MrDiamondDog/FlightDeck/firmware/FlightDeck/src/img.hpp

#include <stdint.h>
#include <pgmspace.h>

// 'American', 16x16px
const uint16_t epd_bitmap_American [] PROGMEM = {
	0xffff, 0xffff, 0xffff, 0xffff, 0xffff, 0xffff, 0xffff, 0xffff, 0xffff, 0xffff, 0xffff, 0xffff, 0xffff, 0xffff, 0xffff, 0xffff, 
	0xffff, 0xffff, 0x23f6, 0x23f6, 0x23f6, 0xffff, 0xffff, 0xffff, 0xffff, 0xffff, 0xffff, 0xffff, 0xffff, 0xffff, 0xffff, 0xffff, 
	0xffff, 0xffff, 0x23f6, 0x23f6, 0x23f6, 0x23f6, 0xffff, 0xffff, 0xffff, 0xffff, 0xffff, 0xffff, 0xffff, 0xffff, 0xffff, 0xffff, 
	0xffff, 0xffff, 0xffff, 0x23f6, 0x23f6, 0x23f6, 0x23f6, 0xffff, 0xffff, 0xffff, 0xffff, 0xffff, 0xffff, 0xffff, 0xffff, 0xffff, 
	0xffff, 0xffff, 0xffff, 0x23f6, 0x23f6, 0x23f6, 0x23f6, 0x23f6, 0xffff, 0xffff, 0xffff, 0xffff, 0xffff, 0xffff, 0xffff, 0xffff, 
	0xffff, 0xffff, 0xffff, 0xffff, 0x23f6, 0x23f6, 0x23f6, 0x23f6, 0x23f6, 0xffff, 0xffff, 0xa514, 0xa514, 0xffff, 0xffff, 0xffff, 
	0xffff, 0xffff, 0xffff, 0xffff, 0xffff, 0x23f6, 0x23f6, 0x23f6, 0x23f6, 0xa514, 0xa514, 0xa514, 0xa514, 0xa514, 0xffff, 0xffff, 
	0xffff, 0xffff, 0xffff, 0xffff, 0xffff, 0xffff, 0xffff, 0xffff, 0xa514, 0xa514, 0xa514, 0xa514, 0xffff, 0xffff, 0xffff, 0xffff, 
	0xffff, 0xffff, 0xffff, 0xffff, 0xffff, 0xffff, 0xa514, 0xa514, 0xa514, 0xa514, 0xb924, 0xffff, 0xffff, 0xffff, 0xffff, 0xffff, 
	0xffff, 0xffff, 0xffff, 0xffff, 0xffff, 0xffff, 0xa514, 0xa514, 0xa514, 0xb924, 0xb924, 0xffff, 0xffff, 0xffff, 0xffff, 0xffff, 
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
const uint16_t* airline_imgs[8] = {
	epd_bitmap_American,
	epd_bitmap_Delta,
	epd_bitmap_Frontier,
	epd_bitmap_JetBlue,
	epd_bitmap_Southwest,
	epd_bitmap_Spirit,
	epd_bitmap_United,
	epd_bitmap_Unknown
};
